K4zuki/tinyI2C/gui/tinyI2Cgui.py

# -*- coding: utf-8 -*-

# Form implementation generated from reading ui file 'tinyI2C.ui'
#
# Created: Mon Feb 02 18:19:01 2015
#      by: PyQt4 UI code generator 4.11.3
#
# WARNING! All changes made in this file will be lost!

from PyQt5 import QtCore, QtGui, QtWidgets

try:
    _fromUtf8 = QtCore.QString.fromUtf8
except AttributeError:
    def _fromUtf8(s):
        return s

try:
    _encoding = QtWidgets.QApplication.UnicodeUTF8

    def _translate(context, text, disambig):
        return QtWidgets.QApplication.translate(context, text, disambig, _encoding)
except AttributeError:
    def _translate(context, text, disambig):
        return QtWidgets.QApplication.translate(context, text, disambig)


class Ui_Form(object):

    def setupUi(self, Form):
        Form.setObjectName(_fromUtf8("Form"))
        Form.resize(726, 826)
        Form.setMaximumSize(QtCore.QSize(1006, 984))
        font = QtGui.QFont()
        font.setPointSize(12)
        Form.setFont(font)
        self.gridLayout = QtWidgets.QGridLayout(Form)
        self.gridLayout.setObjectName(_fromUtf8("gridLayout"))
        self.conport_box = QtWidgets.QGroupBox(Form)
        font = QtGui.QFont()
        font.setPointSize(12)
        self.conport_box.setFont(font)
        self.conport_box.setFlat(False)
        self.conport_box.setCheckable(False)
        self.conport_box.setObjectName(_fromUtf8("conport_box"))
        self.horizontalLayout = QtWidgets.QHBoxLayout(self.conport_box)
        self.horizontalLayout.setObjectName(_fromUtf8("horizontalLayout"))
        self.getPortBtn = QtWidgets.QPushButton(self.conport_box)
        self.getPortBtn.setObjectName(_fromUtf8("getPortBtn"))
        self.horizontalLayout.addWidget(self.getPortBtn)
        self.portList = QtWidgets.QComboBox(self.conport_box)
        font = QtGui.QFont()
        font.setPointSize(12)
        self.portList.setFont(font)
        self.portList.setObjectName(_fromUtf8("portList"))
        self.horizontalLayout.addWidget(self.portList)
        self.gridLayout.addWidget(self.conport_box, 0, 0, 1, 1)
        self.log_box = QtWidgets.QGroupBox(Form)
        font = QtGui.QFont()
        font.setPointSize(12)
        self.log_box.setFont(font)
        self.log_box.setObjectName(_fromUtf8("log_box"))
        self.verticalLayout_9 = QtWidgets.QVBoxLayout(self.log_box)
        self.verticalLayout_9.setObjectName(_fromUtf8("verticalLayout_9"))
        self.log_text = QtWidgets.QPlainTextEdit(self.log_box)
        self.log_text.setVerticalScrollBarPolicy(QtCore.Qt.ScrollBarAlwaysOn)
        self.log_text.setReadOnly(True)
        self.log_text.setCenterOnScroll(True)
        self.log_text.setObjectName(_fromUtf8("log_text"))
        self.verticalLayout_9.addWidget(self.log_text)
        self.gridLayout.addWidget(self.log_box, 5, 0, 1, 1)
        self.i2c_box = QtWidgets.QGroupBox(Form)
        font = QtGui.QFont()
        font.setPointSize(12)
        self.i2c_box.setFont(font)
        self.i2c_box.setObjectName(_fromUtf8("i2c_box"))
        self.horizontalLayout_6 = QtWidgets.QHBoxLayout(self.i2c_box)
        self.horizontalLayout_6.setObjectName(_fromUtf8("horizontalLayout_6"))
        self.i2c1_box = QtWidgets.QGroupBox(self.i2c_box)
        font = QtGui.QFont()
        font.setPointSize(12)
        self.i2c1_box.setFont(font)
        self.i2c1_box.setObjectName(_fromUtf8("i2c1_box"))
        self.verticalLayout = QtWidgets.QVBoxLayout(self.i2c1_box)
        self.verticalLayout.setObjectName(_fromUtf8("verticalLayout"))
        self.base_CH1 = HexSpinBox(self.i2c1_box)
        self.base_CH1.setSuffix(_fromUtf8(""))
        self.base_CH1.setPrefix(_fromUtf8(""))
        self.base_CH1.setMaximum(255)
        self.base_CH1.setSingleStep(2)
        self.base_CH1.setProperty("value", 144)
        self.base_CH1.setObjectName(_fromUtf8("base_CH1"))
        self.verticalLayout.addWidget(self.base_CH1)
        self.reg_CH1 = HexSpinBox(self.i2c1_box)
        self.reg_CH1.setSuffix(_fromUtf8(""))
        self.reg_CH1.setPrefix(_fromUtf8(""))
        self.reg_CH1.setMaximum(255)
        self.reg_CH1.setObjectName(_fromUtf8("reg_CH1"))
        self.verticalLayout.addWidget(self.reg_CH1)
        self.readbtn_CH1 = QtWidgets.QPushButton(self.i2c1_box)
        self.readbtn_CH1.setObjectName(_fromUtf8("readbtn_CH1"))
        self.verticalLayout.addWidget(self.readbtn_CH1)
        self.read_CH1 = HexSpinBox(self.i2c1_box)
        self.read_CH1.setEnabled(False)
        self.read_CH1.setSuffix(_fromUtf8(""))
        self.read_CH1.setPrefix(_fromUtf8(""))
        self.read_CH1.setMaximum(255)
        self.read_CH1.setObjectName(_fromUtf8("read_CH1"))
        self.verticalLayout.addWidget(self.read_CH1)
        self.writebtn_CH1 = QtWidgets.QPushButton(self.i2c1_box)
        self.writebtn_CH1.setObjectName(_fromUtf8("writebtn_CH1"))
        self.verticalLayout.addWidget(self.writebtn_CH1)
        self.write_CH1 = HexSpinBox(self.i2c1_box)
        self.write_CH1.setSuffix(_fromUtf8(""))
        self.write_CH1.setPrefix(_fromUtf8(""))
        self.write_CH1.setMaximum(255)
        self.write_CH1.setObjectName(_fromUtf8("write_CH1"))
        self.verticalLayout.addWidget(self.write_CH1)
        spacerItem = QtWidgets.QSpacerItem(20, 40, QtWidgets.QSizePolicy.Minimum,
                                           QtWidgets.QSizePolicy.MinimumExpanding)
        self.verticalLayout.addItem(spacerItem)
        self.horizontalLayout_6.addWidget(self.i2c1_box)
        self.i2c2_box = QtWidgets.QGroupBox(self.i2c_box)
        font = QtGui.QFont()
        font.setPointSize(12)
        self.i2c2_box.setFont(font)
        self.i2c2_box.setObjectName(_fromUtf8("i2c2_box"))
        self.verticalLayout_5 = QtWidgets.QVBoxLayout(self.i2c2_box)
        self.verticalLayout_5.setObjectName(_fromUtf8("verticalLayout_5"))
        self.base_CH2 = HexSpinBox(self.i2c2_box)
        self.base_CH2.setSuffix(_fromUtf8(""))
        self.base_CH2.setPrefix(_fromUtf8(""))
        self.base_CH2.setMaximum(255)
        self.base_CH2.setSingleStep(2)
        self.base_CH2.setProperty("value", 144)
        self.base_CH2.setObjectName(_fromUtf8("base_CH2"))
        self.verticalLayout_5.addWidget(self.base_CH2)
        self.reg_CH2 = HexSpinBox(self.i2c2_box)
        self.reg_CH2.setSuffix(_fromUtf8(""))
        self.reg_CH2.setPrefix(_fromUtf8(""))
        self.reg_CH2.setMaximum(255)
        self.reg_CH2.setObjectName(_fromUtf8("reg_CH2"))
        self.verticalLayout_5.addWidget(self.reg_CH2)
        self.readbtn_CH2 = QtWidgets.QPushButton(self.i2c2_box)
        self.readbtn_CH2.setObjectName(_fromUtf8("readbtn_CH2"))
        self.verticalLayout_5.addWidget(self.readbtn_CH2)
        self.read_CH2 = HexSpinBox(self.i2c2_box)
        self.read_CH2.setEnabled(False)
        self.read_CH2.setSuffix(_fromUtf8(""))
        self.read_CH2.setPrefix(_fromUtf8(""))
        self.read_CH2.setMaximum(255)
        self.read_CH2.setObjectName(_fromUtf8("read_CH2"))
        self.verticalLayout_5.addWidget(self.read_CH2)
        self.writebtn_CH2 = QtWidgets.QPushButton(self.i2c2_box)
        self.writebtn_CH2.setObjectName(_fromUtf8("writebtn_CH2"))
        self.verticalLayout_5.addWidget(self.writebtn_CH2)
        self.write_CH2 = HexSpinBox(self.i2c2_box)
        self.write_CH2.setSuffix(_fromUtf8(""))
        self.write_CH2.setPrefix(_fromUtf8(""))
        self.write_CH2.setMaximum(255)
        self.write_CH2.setObjectName(_fromUtf8("write_CH2"))
        self.verticalLayout_5.addWidget(self.write_CH2)
        spacerItem1 = QtWidgets.QSpacerItem(20, 40, QtWidgets.QSizePolicy.Minimum,
                                            QtWidgets.QSizePolicy.MinimumExpanding)
        self.verticalLayout_5.addItem(spacerItem1)
        self.horizontalLayout_6.addWidget(self.i2c2_box)
        self.i2c3_box = QtWidgets.QGroupBox(self.i2c_box)
        font = QtGui.QFont()
        font.setPointSize(12)
        self.i2c3_box.setFont(font)
        self.i2c3_box.setObjectName(_fromUtf8("i2c3_box"))
        self.verticalLayout_6 = QtWidgets.QVBoxLayout(self.i2c3_box)
        self.verticalLayout_6.setObjectName(_fromUtf8("verticalLayout_6"))
        self.base_CH3 = HexSpinBox(self.i2c3_box)
        self.base_CH3.setSuffix(_fromUtf8(""))
        self.base_CH3.setPrefix(_fromUtf8(""))
        self.base_CH3.setMaximum(255)
        self.base_CH3.setSingleStep(2)
        self.base_CH3.setProperty("value", 144)
        self.base_CH3.setObjectName(_fromUtf8("base_CH3"))
        self.verticalLayout_6.addWidget(self.base_CH3)
        self.reg_CH3 = HexSpinBox(self.i2c3_box)
        self.reg_CH3.setSuffix(_fromUtf8(""))
        self.reg_CH3.setPrefix(_fromUtf8(""))
        self.reg_CH3.setMaximum(255)
        self.reg_CH3.setObjectName(_fromUtf8("reg_CH3"))
        self.verticalLayout_6.addWidget(self.reg_CH3)
        self.readbtn_CH3 = QtWidgets.QPushButton(self.i2c3_box)
        self.readbtn_CH3.setObjectName(_fromUtf8("readbtn_CH3"))
        self.verticalLayout_6.addWidget(self.readbtn_CH3)
        self.read_CH3 = HexSpinBox(self.i2c3_box)
        self.read_CH3.setEnabled(False)
        self.read_CH3.setSuffix(_fromUtf8(""))
        self.read_CH3.setPrefix(_fromUtf8(""))
        self.read_CH3.setMaximum(255)
        self.read_CH3.setObjectName(_fromUtf8("read_CH3"))
        self.verticalLayout_6.addWidget(self.read_CH3)
        self.writebtn_CH3 = QtWidgets.QPushButton(self.i2c3_box)
        self.writebtn_CH3.setObjectName(_fromUtf8("writebtn_CH3"))
        self.verticalLayout_6.addWidget(self.writebtn_CH3)
        self.write_CH3 = HexSpinBox(self.i2c3_box)
        self.write_CH3.setSuffix(_fromUtf8(""))
        self.write_CH3.setPrefix(_fromUtf8(""))
        self.write_CH3.setMaximum(255)
        self.write_CH3.setObjectName(_fromUtf8("write_CH3"))
        self.verticalLayout_6.addWidget(self.write_CH3)
        spacerItem2 = QtWidgets.QSpacerItem(20, 40, QtWidgets.QSizePolicy.Minimum, QtWidgets.QSizePolicy.Expanding)
        self.verticalLayout_6.addItem(spacerItem2)
        self.horizontalLayout_6.addWidget(self.i2c3_box)
        self.i2c4_box = QtWidgets.QGroupBox(self.i2c_box)
        font = QtGui.QFont()
        font.setPointSize(12)
        self.i2c4_box.setFont(font)
        self.i2c4_box.setObjectName(_fromUtf8("i2c4_box"))
        self.verticalLayout_7 = QtWidgets.QVBoxLayout(self.i2c4_box)
        self.verticalLayout_7.setObjectName(_fromUtf8("verticalLayout_7"))
        self.base_CH4 = HexSpinBox(self.i2c4_box)
        self.base_CH4.setSuffix(_fromUtf8(""))
        self.base_CH4.setPrefix(_fromUtf8(""))
        self.base_CH4.setMaximum(255)
        self.base_CH4.setSingleStep(2)
        self.base_CH4.setProperty("value", 144)
        self.base_CH4.setObjectName(_fromUtf8("base_CH4"))
        self.verticalLayout_7.addWidget(self.base_CH4)
        self.reg_CH4 = HexSpinBox(self.i2c4_box)
        self.reg_CH4.setSuffix(_fromUtf8(""))
        self.reg_CH4.setPrefix(_fromUtf8(""))
        self.reg_CH4.setMaximum(255)
        self.reg_CH4.setObjectName(_fromUtf8("reg_CH4"))
        self.verticalLayout_7.addWidget(self.reg_CH4)
        self.readbtn_CH4 = QtWidgets.QPushButton(self.i2c4_box)
        self.readbtn_CH4.setObjectName(_fromUtf8("readbtn_CH4"))
        self.verticalLayout_7.addWidget(self.readbtn_CH4)
        self.read_CH4 = HexSpinBox(self.i2c4_box)
        self.read_CH4.setEnabled(False)
        self.read_CH4.setSuffix(_fromUtf8(""))
        self.read_CH4.setPrefix(_fromUtf8(""))
        self.read_CH4.setMaximum(255)
        self.read_CH4.setObjectName(_fromUtf8("read_CH4"))
        self.verticalLayout_7.addWidget(self.read_CH4)
        self.writebtn_CH4 = QtWidgets.QPushButton(self.i2c4_box)
        self.writebtn_CH4.setObjectName(_fromUtf8("writebtn_CH4"))
        self.verticalLayout_7.addWidget(self.writebtn_CH4)
        self.write_CH4 = HexSpinBox(self.i2c4_box)
        self.write_CH4.setSuffix(_fromUtf8(""))
        self.write_CH4.setPrefix(_fromUtf8(""))
        self.write_CH4.setMaximum(255)
        self.write_CH4.setObjectName(_fromUtf8("write_CH4"))
        self.verticalLayout_7.addWidget(self.write_CH4)
        spacerItem3 = QtWidgets.QSpacerItem(20, 40, QtWidgets.QSizePolicy.Minimum, QtWidgets.QSizePolicy.Expanding)
        self.verticalLayout_7.addItem(spacerItem3)
        self.horizontalLayout_6.addWidget(self.i2c4_box)
        self.spi_box = QtWidgets.QGroupBox(self.i2c_box)
        font = QtGui.QFont()
        font.setPointSize(12)
        self.spi_box.setFont(font)
        self.spi_box.setObjectName(_fromUtf8("spi_box"))
        self.verticalLayout_10 = QtWidgets.QVBoxLayout(self.spi_box)
        self.verticalLayout_10.setObjectName(_fromUtf8("verticalLayout_10"))
        self.base_SPI = HexSpinBox(self.spi_box)
        self.base_SPI.setSuffix(_fromUtf8(""))
        self.base_SPI.setPrefix(_fromUtf8(""))
        self.base_SPI.setMaximum(255)
        self.base_SPI.setProperty("value", 144)
        self.base_SPI.setObjectName(_fromUtf8("base_SPI"))
        self.verticalLayout_10.addWidget(self.base_SPI)
        self.reg_SPI = HexSpinBox(self.spi_box)
        self.reg_SPI.setSuffix(_fromUtf8(""))
        self.reg_SPI.setPrefix(_fromUtf8(""))
        self.reg_SPI.setMaximum(255)
        self.reg_SPI.setObjectName(_fromUtf8("reg_SPI"))
        self.verticalLayout_10.addWidget(self.reg_SPI)
        self.readbtn_SPI = QtWidgets.QPushButton(self.spi_box)
        self.readbtn_SPI.setObjectName(_fromUtf8("readbtn_SPI"))
        self.verticalLayout_10.addWidget(self.readbtn_SPI)
        self.read_SPI = HexSpinBox(self.spi_box)
        self.read_SPI.setEnabled(False)
        self.read_SPI.setSuffix(_fromUtf8(""))
        self.read_SPI.setPrefix(_fromUtf8(""))
        self.read_SPI.setMaximum(255)
        self.read_SPI.setObjectName(_fromUtf8("read_SPI"))
        self.verticalLayout_10.addWidget(self.read_SPI)
        self.writebtn_SPI = QtWidgets.QPushButton(self.spi_box)
        self.writebtn_SPI.setObjectName(_fromUtf8("writebtn_SPI"))
        self.verticalLayout_10.addWidget(self.writebtn_SPI)
        self.write_SPI = HexSpinBox(self.spi_box)
        self.write_SPI.setSuffix(_fromUtf8(""))
        self.write_SPI.setPrefix(_fromUtf8(""))
        self.write_SPI.setMaximum(255)
        self.write_SPI.setObjectName(_fromUtf8("write_SPI"))
        self.verticalLayout_10.addWidget(self.write_SPI)
        spacerItem4 = QtWidgets.QSpacerItem(20, 40, QtWidgets.QSizePolicy.Minimum, QtWidgets.QSizePolicy.Expanding)
        self.verticalLayout_10.addItem(spacerItem4)
        self.horizontalLayout_6.addWidget(self.spi_box)
        self.gridLayout.addWidget(self.i2c_box, 1, 0, 1, 1)
        self.regixters_box = QtWidgets.QGroupBox(Form)
        self.regixters_box.setObjectName(_fromUtf8("regixters_box"))
        self.verticalLayout_2 = QtWidgets.QVBoxLayout(self.regixters_box)
        self.verticalLayout_2.setObjectName(_fromUtf8("verticalLayout_2"))
        self.registers_tab = QtWidgets.QTabWidget(self.regixters_box)
        self.registers_tab.setObjectName(_fromUtf8("registers_tab"))
        self.tab = QtWidgets.QWidget()
        self.tab.setObjectName(_fromUtf8("tab"))
        self.verticalLayout_11 = QtWidgets.QVBoxLayout(self.tab)
        self.verticalLayout_11.setObjectName(_fromUtf8("verticalLayout_11"))
        self.reg0_box = QtWidgets.QGroupBox(self.tab)
        self.reg0_box.setObjectName(_fromUtf8("reg0_box"))
        self.gridLayout_2 = QtWidgets.QGridLayout(self.reg0_box)
        self.gridLayout_2.setObjectName(_fromUtf8("gridLayout_2"))
        self.readbtn_reg0 = QtWidgets.QPushButton(self.reg0_box)
        self.readbtn_reg0.setObjectName(_fromUtf8("readbtn_reg0"))
        self.gridLayout_2.addWidget(self.readbtn_reg0, 1, 8, 1, 1)
        self.read_reg0 = HexSpinBox(self.reg0_box)
        self.read_reg0.setEnabled(False)
        self.read_reg0.setMaximum(255)
        self.read_reg0.setObjectName(_fromUtf8("read_reg0"))
        self.gridLayout_2.addWidget(self.read_reg0, 1, 9, 1, 1)
        self.writebtn_reg0 = QtWidgets.QPushButton(self.reg0_box)
        self.writebtn_reg0.setEnabled(False)
        self.writebtn_reg0.setObjectName(_fromUtf8("writebtn_reg0"))
        self.gridLayout_2.addWidget(self.writebtn_reg0, 1, 10, 1, 1)
        self.write_reg0 = HexSpinBox(self.reg0_box)
        self.write_reg0.setEnabled(False)
        self.write_reg0.setMaximum(255)
        self.write_reg0.setObjectName(_fromUtf8("write_reg0"))
        self.gridLayout_2.addWidget(self.write_reg0, 1, 11, 1, 1)
        self.label_8 = QtWidgets.QLabel(self.reg0_box)
        self.label_8.setAlignment(QtCore.Qt.AlignCenter)
        self.label_8.setObjectName(_fromUtf8("label_8"))
        self.gridLayout_2.addWidget(self.label_8, 0, 7, 1, 1)
        self.label = QtWidgets.QLabel(self.reg0_box)
        self.label.setAlignment(QtCore.Qt.AlignCenter)
        self.label.setObjectName(_fromUtf8("label"))
        self.gridLayout_2.addWidget(self.label, 0, 0, 1, 1)
        self.label_7 = QtWidgets.QLabel(self.reg0_box)
        self.label_7.setAlignment(QtCore.Qt.AlignCenter)
        self.label_7.setObjectName(_fromUtf8("label_7"))
        self.gridLayout_2.addWidget(self.label_7, 0, 6, 1, 1)
        self.label_6 = QtWidgets.QLabel(self.reg0_box)
        self.label_6.setAlignment(QtCore.Qt.AlignCenter)
        self.label_6.setObjectName(_fromUtf8("label_6"))
        self.gridLayout_2.addWidget(self.label_6, 0, 5, 1, 1)
        self.label_5 = QtWidgets.QLabel(self.reg0_box)
        self.label_5.setAlignment(QtCore.Qt.AlignCenter)
        self.label_5.setObjectName(_fromUtf8("label_5"))
        self.gridLayout_2.addWidget(self.label_5, 0, 4, 1, 1)
        self.label_4 = QtWidgets.QLabel(self.reg0_box)
        self.label_4.setAlignment(QtCore.Qt.AlignCenter)
        self.label_4.setObjectName(_fromUtf8("label_4"))
        self.gridLayout_2.addWidget(self.label_4, 0, 3, 1, 1)
        self.label_3 = QtWidgets.QLabel(self.reg0_box)
        self.label_3.setAlignment(QtCore.Qt.AlignCenter)
        self.label_3.setObjectName(_fromUtf8("label_3"))
        self.gridLayout_2.addWidget(self.label_3, 0, 2, 1, 1)
        self.label_2 = QtWidgets.QLabel(self.reg0_box)
        self.label_2.setAlignment(QtCore.Qt.AlignCenter)
        self.label_2.setObjectName(_fromUtf8("label_2"))
        self.gridLayout_2.addWidget(self.label_2, 0, 1, 1, 1)
        self.reg00 = QtWidgets.QPushButton(self.reg0_box)
        self.reg00.setEnabled(False)
        self.reg00.setMinimumSize(QtCore.QSize(40, 0))
        font = QtGui.QFont()
        font.setPointSize(20)
        self.reg00.setFont(font)
        self.reg00.setCheckable(True)
        self.reg00.setFlat(True)
        self.reg00.setObjectName(_fromUtf8("reg00"))
        self.gridLayout_2.addWidget(self.reg00, 1, 7, 1, 1)
        self.reg01 = QtWidgets.QPushButton(self.reg0_box)
        self.reg01.setEnabled(False)
        self.reg01.setMinimumSize(QtCore.QSize(40, 0))
        font = QtGui.QFont()
        font.setPointSize(20)
        self.reg01.setFont(font)
        self.reg01.setCheckable(True)
        self.reg01.setFlat(True)
        self.reg01.setObjectName(_fromUtf8("reg01"))
        self.gridLayout_2.addWidget(self.reg01, 1, 6, 1, 1)
        self.reg02 = QtWidgets.QPushButton(self.reg0_box)
        self.reg02.setEnabled(False)
        self.reg02.setMinimumSize(QtCore.QSize(40, 0))
        font = QtGui.QFont()
        font.setPointSize(20)
        self.reg02.setFont(font)
        self.reg02.setCheckable(True)
        self.reg02.setFlat(True)
        self.reg02.setObjectName(_fromUtf8("reg02"))
        self.gridLayout_2.addWidget(self.reg02, 1, 5, 1, 1)
        self.reg03 = QtWidgets.QPushButton(self.reg0_box)
        self.reg03.setEnabled(False)
        self.reg03.setMinimumSize(QtCore.QSize(40, 0))
        font = QtGui.QFont()
        font.setPointSize(20)
        self.reg03.setFont(font)
        self.reg03.setCheckable(True)
        self.reg03.setFlat(True)
        self.reg03.setObjectName(_fromUtf8("reg03"))
        self.gridLayout_2.addWidget(self.reg03, 1, 4, 1, 1)
        self.reg04 = QtWidgets.QPushButton(self.reg0_box)
        self.reg04.setEnabled(False)
        self.reg04.setMinimumSize(QtCore.QSize(40, 0))
        font = QtGui.QFont()
        font.setPointSize(20)
        self.reg04.setFont(font)
        self.reg04.setCheckable(True)
        self.reg04.setFlat(True)
        self.reg04.setObjectName(_fromUtf8("reg04"))
        self.gridLayout_2.addWidget(self.reg04, 1, 3, 1, 1)
        self.reg05 = QtWidgets.QPushButton(self.reg0_box)
        self.reg05.setEnabled(False)
        self.reg05.setMinimumSize(QtCore.QSize(40, 0))
        font = QtGui.QFont()
        font.setPointSize(20)
        self.reg05.setFont(font)
        self.reg05.setCheckable(True)
        self.reg05.setFlat(True)
        self.reg05.setObjectName(_fromUtf8("reg05"))
        self.gridLayout_2.addWidget(self.reg05, 1, 2, 1, 1)
        self.reg06 = QtWidgets.QPushButton(self.reg0_box)
        self.reg06.setEnabled(False)
        self.reg06.setMinimumSize(QtCore.QSize(40, 0))
        font = QtGui.QFont()
        font.setPointSize(20)
        self.reg06.setFont(font)
        self.reg06.setCheckable(True)
        self.reg06.setFlat(True)
        self.reg06.setObjectName(_fromUtf8("reg06"))
        self.gridLayout_2.addWidget(self.reg06, 1, 1, 1, 1)
        self.reg07 = QtWidgets.QPushButton(self.reg0_box)
        self.reg07.setEnabled(False)
        self.reg07.setMinimumSize(QtCore.QSize(40, 0))
        font = QtGui.QFont()
        font.setPointSize(20)
        self.reg07.setFont(font)
        self.reg07.setCheckable(True)
        self.reg07.setFlat(True)
        self.reg07.setObjectName(_fromUtf8("reg07"))
        self.gridLayout_2.addWidget(self.reg07, 1, 0, 1, 1)
        self.verticalLayout_11.addWidget(self.reg0_box)
        self.groupBox = QtWidgets.QGroupBox(self.tab)
        self.groupBox.setTitle(_fromUtf8(""))
        self.groupBox.setObjectName(_fromUtf8("groupBox"))
        self.horizontalLayout_2 = QtWidgets.QHBoxLayout(self.groupBox)
        self.horizontalLayout_2.setObjectName(_fromUtf8("horizontalLayout_2"))
        self.verticalLayout_11.addWidget(self.groupBox)
        self.registers_tab.addTab(self.tab, _fromUtf8(""))
        self.tab_2 = QtWidgets.QWidget()
        self.tab_2.setObjectName(_fromUtf8("tab_2"))
        self.verticalLayout_8 = QtWidgets.QVBoxLayout(self.tab_2)
        self.verticalLayout_8.setObjectName(_fromUtf8("verticalLayout_8"))
        self.reg1_box = QtWidgets.QGroupBox(self.tab_2)
        self.reg1_box.setObjectName(_fromUtf8("reg1_box"))
        self.gridLayout_3 = QtWidgets.QGridLayout(self.reg1_box)
        self.gridLayout_3.setObjectName(_fromUtf8("gridLayout_3"))
        self.label_15 = QtWidgets.QLabel(self.reg1_box)
        self.label_15.setAlignment(QtCore.Qt.AlignCenter)
        self.label_15.setObjectName(_fromUtf8("label_15"))
        self.gridLayout_3.addWidget(self.label_15, 0, 0, 1, 1)
        self.label_13 = QtWidgets.QLabel(self.reg1_box)
        self.label_13.setAlignment(QtCore.Qt.AlignCenter)
        self.label_13.setObjectName(_fromUtf8("label_13"))
        self.gridLayout_3.addWidget(self.label_13, 0, 1, 1, 1)
        self.label_16 = QtWidgets.QLabel(self.reg1_box)
        self.label_16.setAlignment(QtCore.Qt.AlignCenter)
        self.label_16.setObjectName(_fromUtf8("label_16"))
        self.gridLayout_3.addWidget(self.label_16, 0, 2, 1, 1)
        self.label_12 = QtWidgets.QLabel(self.reg1_box)
        self.label_12.setAlignment(QtCore.Qt.AlignCenter)
        self.label_12.setObjectName(_fromUtf8("label_12"))
        self.gridLayout_3.addWidget(self.label_12, 0, 3, 1, 1)
        self.label_9 = QtWidgets.QLabel(self.reg1_box)
        self.label_9.setAlignment(QtCore.Qt.AlignCenter)
        self.label_9.setObjectName(_fromUtf8("label_9"))
        self.gridLayout_3.addWidget(self.label_9, 0, 4, 1, 1)
        self.label_14 = QtWidgets.QLabel(self.reg1_box)
        self.label_14.setAlignment(QtCore.Qt.AlignCenter)
        self.label_14.setObjectName(_fromUtf8("label_14"))
        self.gridLayout_3.addWidget(self.label_14, 0, 5, 1, 1)
        self.label_11 = QtWidgets.QLabel(self.reg1_box)
        self.label_11.setAlignment(QtCore.Qt.AlignCenter)
        self.label_11.setObjectName(_fromUtf8("label_11"))
        self.gridLayout_3.addWidget(self.label_11, 0, 6, 1, 1)
        self.label_10 = QtWidgets.QLabel(self.reg1_box)
        self.label_10.setAlignment(QtCore.Qt.AlignCenter)
        self.label_10.setObjectName(_fromUtf8("label_10"))
        self.gridLayout_3.addWidget(self.label_10, 0, 7, 1, 1)
        self.reg17 = QtWidgets.QPushButton(self.reg1_box)
        self.reg17.setEnabled(True)
        self.reg17.setMinimumSize(QtCore.QSize(40, 0))
        font = QtGui.QFont()
        font.setPointSize(20)
        self.reg17.setFont(font)
        self.reg17.setCheckable(True)
        self.reg17.setFlat(True)
        self.reg17.setObjectName(_fromUtf8("reg17"))
        self.gridLayout_3.addWidget(self.reg17, 1, 0, 1, 1)
        self.reg16 = QtWidgets.QPushButton(self.reg1_box)
        self.reg16.setEnabled(True)
        self.reg16.setMinimumSize(QtCore.QSize(40, 0))
        font = QtGui.QFont()
        font.setPointSize(20)
        self.reg16.setFont(font)
        self.reg16.setCheckable(True)
        self.reg16.setFlat(True)
        self.reg16.setObjectName(_fromUtf8("reg16"))
        self.gridLayout_3.addWidget(self.reg16, 1, 1, 1, 1)
        self.reg15 = QtWidgets.QPushButton(self.reg1_box)
        self.reg15.setEnabled(True)
        self.reg15.setMinimumSize(QtCore.QSize(40, 0))
        font = QtGui.QFont()
        font.setPointSize(20)
        self.reg15.setFont(font)
        self.reg15.setCheckable(True)
        self.reg15.setFlat(True)
        self.reg15.setObjectName(_fromUtf8("reg15"))
        self.gridLayout_3.addWidget(self.reg15, 1, 2, 1, 1)
        self.reg14 = QtWidgets.QPushButton(self.reg1_box)
        self.reg14.setEnabled(True)
        self.reg14.setMinimumSize(QtCore.QSize(40, 0))
        font = QtGui.QFont()
        font.setPointSize(20)
        self.reg14.setFont(font)
        self.reg14.setCheckable(True)
        self.reg14.setFlat(True)
        self.reg14.setObjectName(_fromUtf8("reg14"))
        self.gridLayout_3.addWidget(self.reg14, 1, 3, 1, 1)
        self.reg13 = QtWidgets.QPushButton(self.reg1_box)
        self.reg13.setEnabled(True)
        self.reg13.setMinimumSize(QtCore.QSize(40, 0))
        font = QtGui.QFont()
        font.setPointSize(20)
        self.reg13.setFont(font)
        self.reg13.setCheckable(True)
        self.reg13.setFlat(True)
        self.reg13.setObjectName(_fromUtf8("reg13"))
        self.gridLayout_3.addWidget(self.reg13, 1, 4, 1, 1)
        self.reg12 = QtWidgets.QPushButton(self.reg1_box)
        self.reg12.setEnabled(True)
        self.reg12.setMinimumSize(QtCore.QSize(40, 0))
        font = QtGui.QFont()
        font.setPointSize(20)
        self.reg12.setFont(font)
        self.reg12.setCheckable(True)
        self.reg12.setFlat(True)
        self.reg12.setObjectName(_fromUtf8("reg12"))
        self.gridLayout_3.addWidget(self.reg12, 1, 5, 1, 1)
        self.reg11 = QtWidgets.QPushButton(self.reg1_box)
        self.reg11.setEnabled(True)
        self.reg11.setMinimumSize(QtCore.QSize(40, 0))
        font = QtGui.QFont()
        font.setPointSize(20)
        self.reg11.setFont(font)
        self.reg11.setCheckable(True)
        self.reg11.setFlat(True)
        self.reg11.setObjectName(_fromUtf8("reg11"))
        self.gridLayout_3.addWidget(self.reg11, 1, 6, 1, 1)
        self.reg10 = QtWidgets.QPushButton(self.reg1_box)
        self.reg10.setEnabled(True)
        self.reg10.setMinimumSize(QtCore.QSize(40, 0))
        font = QtGui.QFont()
        font.setPointSize(20)
        self.reg10.setFont(font)
        self.reg10.setCheckable(True)
        self.reg10.setFlat(True)
        self.reg10.setObjectName(_fromUtf8("reg10"))
        self.gridLayout_3.addWidget(self.reg10, 1, 7, 1, 1)
        self.readbtn_reg1 = QtWidgets.QPushButton(self.reg1_box)
        self.readbtn_reg1.setObjectName(_fromUtf8("readbtn_reg1"))
        self.gridLayout_3.addWidget(self.readbtn_reg1, 1, 8, 1, 1)
        self.read_reg1 = HexSpinBox(self.reg1_box)
        self.read_reg1.setEnabled(False)
        self.read_reg1.setMaximum(255)
        self.read_reg1.setObjectName(_fromUtf8("read_reg1"))
        self.gridLayout_3.addWidget(self.read_reg1, 1, 9, 1, 1)
        self.writebtn_reg1 = QtWidgets.QPushButton(self.reg1_box)
        self.writebtn_reg1.setObjectName(_fromUtf8("writebtn_reg1"))
        self.gridLayout_3.addWidget(self.writebtn_reg1, 1, 10, 1, 1)
        self.write_reg1 = HexSpinBox(self.reg1_box)
        self.write_reg1.setMaximum(255)
        self.write_reg1.setObjectName(_fromUtf8("write_reg1"))
        self.gridLayout_3.addWidget(self.write_reg1, 1, 11, 1, 1)
        self.verticalLayout_8.addWidget(self.reg1_box)
        self.reg3_box = QtWidgets.QGroupBox(self.tab_2)
        self.reg3_box.setObjectName(_fromUtf8("reg3_box"))
        self.gridLayout_7 = QtWidgets.QGridLayout(self.reg3_box)
        self.gridLayout_7.setObjectName(_fromUtf8("gridLayout_7"))
        self.label_47 = QtWidgets.QLabel(self.reg3_box)
        self.label_47.setAlignment(QtCore.Qt.AlignCenter)
        self.label_47.setObjectName(_fromUtf8("label_47"))
        self.gridLayout_7.addWidget(self.label_47, 0, 0, 1, 1)
        self.label_48 = QtWidgets.QLabel(self.reg3_box)
        self.label_48.setAlignment(QtCore.Qt.AlignCenter)
        self.label_48.setObjectName(_fromUtf8("label_48"))
        self.gridLayout_7.addWidget(self.label_48, 0, 2, 1, 1)
        self.label_46 = QtWidgets.QLabel(self.reg3_box)
        self.label_46.setAlignment(QtCore.Qt.AlignCenter)
        self.label_46.setObjectName(_fromUtf8("label_46"))
        self.gridLayout_7.addWidget(self.label_46, 0, 5, 1, 1)
        self.reg36 = QtWidgets.QPushButton(self.reg3_box)
        self.reg36.setMinimumSize(QtCore.QSize(40, 0))
        font = QtGui.QFont()
        font.setPointSize(20)
        self.reg36.setFont(font)
        self.reg36.setCheckable(True)
        self.reg36.setFlat(True)
        self.reg36.setObjectName(_fromUtf8("reg36"))
        self.gridLayout_7.addWidget(self.reg36, 2, 1, 1, 1)
        self.reg35 = QtWidgets.QPushButton(self.reg3_box)
        self.reg35.setMinimumSize(QtCore.QSize(40, 0))
        font = QtGui.QFont()
        font.setPointSize(20)
        self.reg35.setFont(font)
        self.reg35.setCheckable(True)
        self.reg35.setFlat(True)
        self.reg35.setObjectName(_fromUtf8("reg35"))
        self.gridLayout_7.addWidget(self.reg35, 2, 2, 1, 1)
        self.reg34 = QtWidgets.QPushButton(self.reg3_box)
        self.reg34.setMinimumSize(QtCore.QSize(40, 0))
        font = QtGui.QFont()
        font.setPointSize(20)
        self.reg34.setFont(font)
        self.reg34.setCheckable(True)
        self.reg34.setFlat(True)
        self.reg34.setObjectName(_fromUtf8("reg34"))
        self.gridLayout_7.addWidget(self.reg34, 2, 3, 1, 1)
        self.label_41 = QtWidgets.QLabel(self.reg3_box)
        self.label_41.setAlignment(QtCore.Qt.AlignCenter)
        self.label_41.setObjectName(_fromUtf8("label_41"))
        self.gridLayout_7.addWidget(self.label_41, 0, 4, 1, 1)
        self.label_45 = QtWidgets.QLabel(self.reg3_box)
        self.label_45.setAlignment(QtCore.Qt.AlignCenter)
        self.label_45.setObjectName(_fromUtf8("label_45"))
        self.gridLayout_7.addWidget(self.label_45, 0, 1, 1, 1)
        self.write_reg3 = HexSpinBox(self.reg3_box)
        self.write_reg3.setMaximum(255)
        self.write_reg3.setObjectName(_fromUtf8("write_reg3"))
        self.gridLayout_7.addWidget(self.write_reg3, 2, 17, 1, 1)
        self.writebtn_reg3 = QtWidgets.QPushButton(self.reg3_box)
        self.writebtn_reg3.setObjectName(_fromUtf8("writebtn_reg3"))
        self.gridLayout_7.addWidget(self.writebtn_reg3, 2, 16, 1, 1)
        self.readbtn_reg3 = QtWidgets.QPushButton(self.reg3_box)
        self.readbtn_reg3.setObjectName(_fromUtf8("readbtn_reg3"))
        self.gridLayout_7.addWidget(self.readbtn_reg3, 2, 14, 1, 1)
        self.read_reg3 = HexSpinBox(self.reg3_box)
        self.read_reg3.setEnabled(False)
        self.read_reg3.setMaximum(255)
        self.read_reg3.setObjectName(_fromUtf8("read_reg3"))
        self.gridLayout_7.addWidget(self.read_reg3, 2, 15, 1, 1)
        self.label_44 = QtWidgets.QLabel(self.reg3_box)
        self.label_44.setAlignment(QtCore.Qt.AlignCenter)
        self.label_44.setObjectName(_fromUtf8("label_44"))
        self.gridLayout_7.addWidget(self.label_44, 0, 3, 1, 1)
        self.reg30 = QtWidgets.QPushButton(self.reg3_box)
        self.reg30.setMinimumSize(QtCore.QSize(40, 0))
        font = QtGui.QFont()
        font.setPointSize(20)
        self.reg30.setFont(font)
        self.reg30.setCheckable(True)
        self.reg30.setFlat(True)
        self.reg30.setObjectName(_fromUtf8("reg30"))
        self.gridLayout_7.addWidget(self.reg30, 2, 7, 1, 1)
        self.reg33 = QtWidgets.QPushButton(self.reg3_box)
        self.reg33.setMinimumSize(QtCore.QSize(40, 0))
        font = QtGui.QFont()
        font.setPointSize(20)
        self.reg33.setFont(font)
        self.reg33.setCheckable(True)
        self.reg33.setFlat(True)
        self.reg33.setObjectName(_fromUtf8("reg33"))
        self.gridLayout_7.addWidget(self.reg33, 2, 4, 1, 1)
        self.label_42 = QtWidgets.QLabel(self.reg3_box)
        self.label_42.setAlignment(QtCore.Qt.AlignCenter)
        self.label_42.setObjectName(_fromUtf8("label_42"))
        self.gridLayout_7.addWidget(self.label_42, 0, 7, 1, 1)
        self.label_43 = QtWidgets.QLabel(self.reg3_box)
        self.label_43.setAlignment(QtCore.Qt.AlignCenter)
        self.label_43.setObjectName(_fromUtf8("label_43"))
        self.gridLayout_7.addWidget(self.label_43, 0, 6, 1, 1)
        self.reg32 = QtWidgets.QPushButton(self.reg3_box)
        self.reg32.setMinimumSize(QtCore.QSize(40, 0))
        font = QtGui.QFont()
        font.setPointSize(20)
        self.reg32.setFont(font)
        self.reg32.setCheckable(True)
        self.reg32.setFlat(True)
        self.reg32.setObjectName(_fromUtf8("reg32"))
        self.gridLayout_7.addWidget(self.reg32, 2, 5, 1, 1)
        self.reg31 = QtWidgets.QPushButton(self.reg3_box)
        self.reg31.setMinimumSize(QtCore.QSize(40, 0))
        font = QtGui.QFont()
        font.setPointSize(20)
        self.reg31.setFont(font)
        self.reg31.setCheckable(True)
        self.reg31.setFlat(True)
        self.reg31.setObjectName(_fromUtf8("reg31"))
        self.gridLayout_7.addWidget(self.reg31, 2, 6, 1, 1)
        self.reg37 = QtWidgets.QPushButton(self.reg3_box)
        self.reg37.setMinimumSize(QtCore.QSize(40, 0))
        font = QtGui.QFont()
        font.setPointSize(20)
        self.reg37.setFont(font)
        self.reg37.setCheckable(True)
        self.reg37.setFlat(True)
        self.reg37.setObjectName(_fromUtf8("reg37"))
        self.gridLayout_7.addWidget(self.reg37, 2, 0, 1, 1)
        self.verticalLayout_8.addWidget(self.reg3_box)
        self.registers_tab.addTab(self.tab_2, _fromUtf8(""))
        self.tab_3 = QtWidgets.QWidget()
        self.tab_3.setObjectName(_fromUtf8("tab_3"))
        self.verticalLayout_3 = QtWidgets.QVBoxLayout(self.tab_3)
        self.verticalLayout_3.setObjectName(_fromUtf8("verticalLayout_3"))
        self.groupBox_14 = QtWidgets.QGroupBox(self.tab_3)
        self.groupBox_14.setEnabled(False)
        self.groupBox_14.setObjectName(_fromUtf8("groupBox_14"))
        self.gridLayout_6 = QtWidgets.QGridLayout(self.groupBox_14)
        self.gridLayout_6.setObjectName(_fromUtf8("gridLayout_6"))
        self.label_37 = QtWidgets.QLabel(self.groupBox_14)
        self.label_37.setAlignment(QtCore.Qt.AlignCenter)
        self.label_37.setObjectName(_fromUtf8("label_37"))
        self.gridLayout_6.addWidget(self.label_37, 1, 1, 1, 1)
        self.label_40 = QtWidgets.QLabel(self.groupBox_14)
        self.label_40.setAlignment(QtCore.Qt.AlignCenter)
        self.label_40.setObjectName(_fromUtf8("label_40"))
        self.gridLayout_6.addWidget(self.label_40, 1, 2, 1, 1)
        self.label_36 = QtWidgets.QLabel(self.groupBox_14)
        self.label_36.setAlignment(QtCore.Qt.AlignCenter)
        self.label_36.setObjectName(_fromUtf8("label_36"))
        self.gridLayout_6.addWidget(self.label_36, 1, 3, 1, 1)
        self.label_33 = QtWidgets.QLabel(self.groupBox_14)
        self.label_33.setAlignment(QtCore.Qt.AlignCenter)
        self.label_33.setObjectName(_fromUtf8("label_33"))
        self.gridLayout_6.addWidget(self.label_33, 1, 4, 1, 1)
        self.label_38 = QtWidgets.QLabel(self.groupBox_14)
        self.label_38.setAlignment(QtCore.Qt.AlignCenter)
        self.label_38.setObjectName(_fromUtf8("label_38"))
        self.gridLayout_6.addWidget(self.label_38, 1, 5, 1, 1)
        self.label_35 = QtWidgets.QLabel(self.groupBox_14)
        self.label_35.setAlignment(QtCore.Qt.AlignCenter)
        self.label_35.setObjectName(_fromUtf8("label_35"))
        self.gridLayout_6.addWidget(self.label_35, 1, 6, 1, 1)
        self.label_34 = QtWidgets.QLabel(self.groupBox_14)
        self.label_34.setAlignment(QtCore.Qt.AlignCenter)
        self.label_34.setObjectName(_fromUtf8("label_34"))
        self.gridLayout_6.addWidget(self.label_34, 1, 7, 1, 1)
        self.reg22 = QtWidgets.QPushButton(self.groupBox_14)
        self.reg22.setMinimumSize(QtCore.QSize(40, 0))
        font = QtGui.QFont()
        font.setPointSize(20)
        self.reg22.setFont(font)
        self.reg22.setCheckable(True)
        self.reg22.setFlat(True)
        self.reg22.setObjectName(_fromUtf8("reg22"))
        self.gridLayout_6.addWidget(self.reg22, 3, 5, 1, 1)
        self.spinBox_11 = HexSpinBox(self.groupBox_14)
        self.spinBox_11.setMaximum(255)
        self.spinBox_11.setObjectName(_fromUtf8("spinBox_11"))
        self.gridLayout_6.addWidget(self.spinBox_11, 3, 11, 1, 1)
        self.reg24 = QtWidgets.QPushButton(self.groupBox_14)
        self.reg24.setMinimumSize(QtCore.QSize(40, 0))
        font = QtGui.QFont()
        font.setPointSize(20)
        self.reg24.setFont(font)
        self.reg24.setCheckable(True)
        self.reg24.setFlat(True)
        self.reg24.setObjectName(_fromUtf8("reg24"))
        self.gridLayout_6.addWidget(self.reg24, 3, 3, 1, 1)
        self.reg25 = QtWidgets.QPushButton(self.groupBox_14)
        self.reg25.setMinimumSize(QtCore.QSize(40, 0))
        font = QtGui.QFont()
        font.setPointSize(20)
        self.reg25.setFont(font)
        self.reg25.setCheckable(True)
        self.reg25.setFlat(True)
        self.reg25.setObjectName(_fromUtf8("reg25"))
        self.gridLayout_6.addWidget(self.reg25, 3, 2, 1, 1)
        self.read_reg2 = HexSpinBox(self.groupBox_14)
        self.read_reg2.setEnabled(False)
        self.read_reg2.setMaximum(255)
        self.read_reg2.setObjectName(_fromUtf8("read_reg2"))
        self.gridLayout_6.addWidget(self.read_reg2, 3, 9, 1, 1)
        self.readbtn_reg2 = QtWidgets.QPushButton(self.groupBox_14)
        self.readbtn_reg2.setObjectName(_fromUtf8("readbtn_reg2"))
        self.gridLayout_6.addWidget(self.readbtn_reg2, 3, 8, 1, 1)
        self.reg27 = QtWidgets.QPushButton(self.groupBox_14)
        self.reg27.setMinimumSize(QtCore.QSize(40, 0))
        font = QtGui.QFont()
        font.setPointSize(20)
        self.reg27.setFont(font)
        self.reg27.setCheckable(True)
        self.reg27.setFlat(True)
        self.reg27.setObjectName(_fromUtf8("reg27"))
        self.gridLayout_6.addWidget(self.reg27, 3, 0, 1, 1)
        self.reg23 = QtWidgets.QPushButton(self.groupBox_14)
        self.reg23.setMinimumSize(QtCore.QSize(40, 0))
        font = QtGui.QFont()
        font.setPointSize(20)
        self.reg23.setFont(font)
        self.reg23.setCheckable(True)
        self.reg23.setFlat(True)
        self.reg23.setObjectName(_fromUtf8("reg23"))
        self.gridLayout_6.addWidget(self.reg23, 3, 4, 1, 1)
        self.reg20 = QtWidgets.QPushButton(self.groupBox_14)
        self.reg20.setMinimumSize(QtCore.QSize(40, 0))
        font = QtGui.QFont()
        font.setPointSize(20)
        self.reg20.setFont(font)
        self.reg20.setCheckable(True)
        self.reg20.setFlat(True)
        self.reg20.setObjectName(_fromUtf8("reg20"))
        self.gridLayout_6.addWidget(self.reg20, 3, 7, 1, 1)
        self.reg21 = QtWidgets.QPushButton(self.groupBox_14)
        self.reg21.setMinimumSize(QtCore.QSize(40, 0))
        font = QtGui.QFont()
        font.setPointSize(20)
        self.reg21.setFont(font)
        self.reg21.setCheckable(True)
        self.reg21.setFlat(True)
        self.reg21.setObjectName(_fromUtf8("reg21"))
        self.gridLayout_6.addWidget(self.reg21, 3, 6, 1, 1)
        self.reg26 = QtWidgets.QPushButton(self.groupBox_14)
        self.reg26.setMinimumSize(QtCore.QSize(40, 0))
        font = QtGui.QFont()
        font.setPointSize(20)
        self.reg26.setFont(font)
        self.reg26.setCheckable(True)
        self.reg26.setFlat(True)
        self.reg26.setObjectName(_fromUtf8("reg26"))
        self.gridLayout_6.addWidget(self.reg26, 3, 1, 1, 1)
        self.writebtn_reg2 = QtWidgets.QPushButton(self.groupBox_14)
        self.writebtn_reg2.setObjectName(_fromUtf8("writebtn_reg2"))
        self.gridLayout_6.addWidget(self.writebtn_reg2, 3, 10, 1, 1)
        self.label_39 = QtWidgets.QLabel(self.groupBox_14)
        self.label_39.setAlignment(QtCore.Qt.AlignCenter)
        self.label_39.setObjectName(_fromUtf8("label_39"))
        self.gridLayout_6.addWidget(self.label_39, 1, 0, 1, 1)
        self.verticalLayout_3.addWidget(self.groupBox_14)
        self.groupBox_18 = QtWidgets.QGroupBox(self.tab_3)
        self.groupBox_18.setEnabled(False)
        self.groupBox_18.setObjectName(_fromUtf8("groupBox_18"))
        self.gridLayout_8 = QtWidgets.QGridLayout(self.groupBox_18)
        self.gridLayout_8.setObjectName(_fromUtf8("gridLayout_8"))
        self.writebtn_reg4 = QtWidgets.QPushButton(self.groupBox_18)
        self.writebtn_reg4.setObjectName(_fromUtf8("writebtn_reg4"))
        self.gridLayout_8.addWidget(self.writebtn_reg4, 2, 10, 1, 1)
        self.read_reg4 = HexSpinBox(self.groupBox_18)
        self.read_reg4.setEnabled(False)
        self.read_reg4.setMaximum(255)
        self.read_reg4.setObjectName(_fromUtf8("read_reg4"))
        self.gridLayout_8.addWidget(self.read_reg4, 2, 9, 1, 1)
        self.write_reg4 = HexSpinBox(self.groupBox_18)
        self.write_reg4.setMaximum(255)
        self.write_reg4.setObjectName(_fromUtf8("write_reg4"))
        self.gridLayout_8.addWidget(self.write_reg4, 2, 11, 1, 1)
        self.readbtn_reg4 = QtWidgets.QPushButton(self.groupBox_18)
        self.readbtn_reg4.setObjectName(_fromUtf8("readbtn_reg4"))
        self.gridLayout_8.addWidget(self.readbtn_reg4, 2, 8, 1, 1)
        self.label_55 = QtWidgets.QLabel(self.groupBox_18)
        self.label_55.setAlignment(QtCore.Qt.AlignCenter)
        self.label_55.setObjectName(_fromUtf8("label_55"))
        self.gridLayout_8.addWidget(self.label_55, 1, 0, 1, 1)
        self.label_53 = QtWidgets.QLabel(self.groupBox_18)
        self.label_53.setAlignment(QtCore.Qt.AlignCenter)
        self.label_53.setObjectName(_fromUtf8("label_53"))
        self.gridLayout_8.addWidget(self.label_53, 1, 1, 1, 1)
        self.label_56 = QtWidgets.QLabel(self.groupBox_18)
        self.label_56.setAlignment(QtCore.Qt.AlignCenter)
        self.label_56.setObjectName(_fromUtf8("label_56"))
        self.gridLayout_8.addWidget(self.label_56, 1, 2, 1, 1)
        self.label_52 = QtWidgets.QLabel(self.groupBox_18)
        self.label_52.setAlignment(QtCore.Qt.AlignCenter)
        self.label_52.setObjectName(_fromUtf8("label_52"))
        self.gridLayout_8.addWidget(self.label_52, 1, 3, 1, 1)
        self.label_49 = QtWidgets.QLabel(self.groupBox_18)
        self.label_49.setAlignment(QtCore.Qt.AlignCenter)
        self.label_49.setObjectName(_fromUtf8("label_49"))
        self.gridLayout_8.addWidget(self.label_49, 1, 4, 1, 1)
        self.label_54 = QtWidgets.QLabel(self.groupBox_18)
        self.label_54.setAlignment(QtCore.Qt.AlignCenter)
        self.label_54.setObjectName(_fromUtf8("label_54"))
        self.gridLayout_8.addWidget(self.label_54, 1, 5, 1, 1)
        self.label_51 = QtWidgets.QLabel(self.groupBox_18)
        self.label_51.setAlignment(QtCore.Qt.AlignCenter)
        self.label_51.setObjectName(_fromUtf8("label_51"))
        self.gridLayout_8.addWidget(self.label_51, 1, 6, 1, 1)
        self.label_50 = QtWidgets.QLabel(self.groupBox_18)
        self.label_50.setAlignment(QtCore.Qt.AlignCenter)
        self.label_50.setObjectName(_fromUtf8("label_50"))
        self.gridLayout_8.addWidget(self.label_50, 1, 7, 1, 1)
        self.reg47 = QtWidgets.QPushButton(self.groupBox_18)
        self.reg47.setMinimumSize(QtCore.QSize(40, 0))
        font = QtGui.QFont()
        font.setPointSize(20)
        self.reg47.setFont(font)
        self.reg47.setCheckable(True)
        self.reg47.setFlat(True)
        self.reg47.setObjectName(_fromUtf8("reg47"))
        self.gridLayout_8.addWidget(self.reg47, 2, 0, 1, 1)
        self.reg46 = QtWidgets.QPushButton(self.groupBox_18)
        self.reg46.setMinimumSize(QtCore.QSize(40, 0))
        font = QtGui.QFont()
        font.setPointSize(20)
        self.reg46.setFont(font)
        self.reg46.setCheckable(True)
        self.reg46.setFlat(True)
        self.reg46.setObjectName(_fromUtf8("reg46"))
        self.gridLayout_8.addWidget(self.reg46, 2, 1, 1, 1)
        self.reg45 = QtWidgets.QPushButton(self.groupBox_18)
        self.reg45.setMinimumSize(QtCore.QSize(40, 0))
        font = QtGui.QFont()
        font.setPointSize(20)
        self.reg45.setFont(font)
        self.reg45.setCheckable(True)
        self.reg45.setFlat(True)
        self.reg45.setObjectName(_fromUtf8("reg45"))
        self.gridLayout_8.addWidget(self.reg45, 2, 2, 1, 1)
        self.reg44 = QtWidgets.QPushButton(self.groupBox_18)
        self.reg44.setMinimumSize(QtCore.QSize(40, 0))
        font = QtGui.QFont()
        font.setPointSize(20)
        self.reg44.setFont(font)
        self.reg44.setCheckable(True)
        self.reg44.setFlat(True)
        self.reg44.setObjectName(_fromUtf8("reg44"))
        self.gridLayout_8.addWidget(self.reg44, 2, 3, 1, 1)
        self.reg43 = QtWidgets.QPushButton(self.groupBox_18)
        self.reg43.setMinimumSize(QtCore.QSize(40, 0))
        font = QtGui.QFont()
        font.setPointSize(20)
        self.reg43.setFont(font)
        self.reg43.setCheckable(True)
        self.reg43.setFlat(True)
        self.reg43.setObjectName(_fromUtf8("reg43"))
        self.gridLayout_8.addWidget(self.reg43, 2, 4, 1, 1)
        self.reg42 = QtWidgets.QPushButton(self.groupBox_18)
        self.reg42.setMinimumSize(QtCore.QSize(40, 0))
        font = QtGui.QFont()
        font.setPointSize(20)
        self.reg42.setFont(font)
        self.reg42.setCheckable(True)
        self.reg42.setFlat(True)
        self.reg42.setObjectName(_fromUtf8("reg42"))
        self.gridLayout_8.addWidget(self.reg42, 2, 5, 1, 1)
        self.reg41 = QtWidgets.QPushButton(self.groupBox_18)
        self.reg41.setMinimumSize(QtCore.QSize(40, 0))
        font = QtGui.QFont()
        font.setPointSize(20)
        self.reg41.setFont(font)
        self.reg41.setCheckable(True)
        self.reg41.setFlat(True)
        self.reg41.setObjectName(_fromUtf8("reg41"))
        self.gridLayout_8.addWidget(self.reg41, 2, 6, 1, 1)
        self.reg40 = QtWidgets.QPushButton(self.groupBox_18)
        self.reg40.setMinimumSize(QtCore.QSize(40, 0))
        font = QtGui.QFont()
        font.setPointSize(20)
        self.reg40.setFont(font)
        self.reg40.setCheckable(True)
        self.reg40.setFlat(True)
        self.reg40.setObjectName(_fromUtf8("reg40"))
        self.gridLayout_8.addWidget(self.reg40, 2, 7, 1, 1)
        self.verticalLayout_3.addWidget(self.groupBox_18)
        self.registers_tab.addTab(self.tab_3, _fromUtf8(""))
        self.tab_6 = QtWidgets.QWidget()
        self.tab_6.setObjectName(_fromUtf8("tab_6"))
        self.verticalLayout_12 = QtWidgets.QVBoxLayout(self.tab_6)
        self.verticalLayout_12.setObjectName(_fromUtf8("verticalLayout_12"))
        self.groupBox_17 = QtWidgets.QGroupBox(self.tab_6)
        self.groupBox_17.setEnabled(True)
        self.groupBox_17.setObjectName(_fromUtf8("groupBox_17"))
        self.gridLayout_9 = QtWidgets.QGridLayout(self.groupBox_17)
        self.gridLayout_9.setObjectName(_fromUtf8("gridLayout_9"))
        self.label_61 = QtWidgets.QLabel(self.groupBox_17)
        self.label_61.setAlignment(QtCore.Qt.AlignCenter)
        self.label_61.setObjectName(_fromUtf8("label_61"))
        self.gridLayout_9.addWidget(self.label_61, 0, 1, 1, 1)
        self.label_59 = QtWidgets.QLabel(self.groupBox_17)
        self.label_59.setAlignment(QtCore.Qt.AlignCenter)
        self.label_59.setObjectName(_fromUtf8("label_59"))
        self.gridLayout_9.addWidget(self.label_59, 0, 6, 1, 1)
        self.label_60 = QtWidgets.QLabel(self.groupBox_17)
        self.label_60.setAlignment(QtCore.Qt.AlignCenter)
        self.label_60.setObjectName(_fromUtf8("label_60"))
        self.gridLayout_9.addWidget(self.label_60, 0, 3, 1, 1)
        self.label_62 = QtWidgets.QLabel(self.groupBox_17)
        self.label_62.setAlignment(QtCore.Qt.AlignCenter)
        self.label_62.setObjectName(_fromUtf8("label_62"))
        self.gridLayout_9.addWidget(self.label_62, 0, 5, 1, 1)
        self.label_57 = QtWidgets.QLabel(self.groupBox_17)
        self.label_57.setAlignment(QtCore.Qt.AlignCenter)
        self.label_57.setObjectName(_fromUtf8("label_57"))
        self.gridLayout_9.addWidget(self.label_57, 0, 4, 1, 1)
        self.label_64 = QtWidgets.QLabel(self.groupBox_17)
        self.label_64.setAlignment(QtCore.Qt.AlignCenter)
        self.label_64.setObjectName(_fromUtf8("label_64"))
        self.gridLayout_9.addWidget(self.label_64, 0, 2, 1, 1)
        self.readbtn_reg5 = QtWidgets.QPushButton(self.groupBox_17)
        self.readbtn_reg5.setEnabled(True)
        self.readbtn_reg5.setObjectName(_fromUtf8("readbtn_reg5"))
        self.gridLayout_9.addWidget(self.readbtn_reg5, 1, 8, 1, 1)
        self.write_reg5 = HexSpinBox(self.groupBox_17)
        self.write_reg5.setEnabled(False)
        self.write_reg5.setMaximum(255)
        self.write_reg5.setObjectName(_fromUtf8("write_reg5"))
        self.gridLayout_9.addWidget(self.write_reg5, 1, 11, 1, 1)
        self.writebtn_reg5 = QtWidgets.QPushButton(self.groupBox_17)
        self.writebtn_reg5.setEnabled(True)
        self.writebtn_reg5.setObjectName(_fromUtf8("writebtn_reg5"))
        self.gridLayout_9.addWidget(self.writebtn_reg5, 1, 10, 1, 1)
        self.label_63 = QtWidgets.QLabel(self.groupBox_17)
        self.label_63.setAlignment(QtCore.Qt.AlignCenter)
        self.label_63.setObjectName(_fromUtf8("label_63"))
        self.gridLayout_9.addWidget(self.label_63, 0, 0, 1, 1)
        self.read_reg5 = HexSpinBox(self.groupBox_17)
        self.read_reg5.setEnabled(False)
        self.read_reg5.setMaximum(255)
        self.read_reg5.setObjectName(_fromUtf8("read_reg5"))
        self.gridLayout_9.addWidget(self.read_reg5, 1, 9, 1, 1)
        self.label_58 = QtWidgets.QLabel(self.groupBox_17)
        self.label_58.setAlignment(QtCore.Qt.AlignCenter)
        self.label_58.setObjectName(_fromUtf8("label_58"))
        self.gridLayout_9.addWidget(self.label_58, 0, 7, 1, 1)
        self.reg51 = QtWidgets.QPushButton(self.groupBox_17)
        self.reg51.setEnabled(False)
        self.reg51.setMinimumSize(QtCore.QSize(40, 0))
        font = QtGui.QFont()
        font.setPointSize(20)
        self.reg51.setFont(font)
        self.reg51.setCheckable(True)
        self.reg51.setFlat(True)
        self.reg51.setObjectName(_fromUtf8("reg51"))
        self.gridLayout_9.addWidget(self.reg51, 1, 6, 1, 1)
        self.reg52 = QtWidgets.QPushButton(self.groupBox_17)
        self.reg52.setEnabled(False)
        self.reg52.setMinimumSize(QtCore.QSize(40, 0))
        font = QtGui.QFont()
        font.setPointSize(20)
        self.reg52.setFont(font)
        self.reg52.setCheckable(True)
        self.reg52.setFlat(True)
        self.reg52.setObjectName(_fromUtf8("reg52"))
        self.gridLayout_9.addWidget(self.reg52, 1, 5, 1, 1)
        self.reg53 = QtWidgets.QPushButton(self.groupBox_17)
        self.reg53.setEnabled(False)
        self.reg53.setMinimumSize(QtCore.QSize(40, 0))
        font = QtGui.QFont()
        font.setPointSize(20)
        self.reg53.setFont(font)
        self.reg53.setCheckable(True)
        self.reg53.setFlat(True)
        self.reg53.setObjectName(_fromUtf8("reg53"))
        self.gridLayout_9.addWidget(self.reg53, 1, 4, 1, 1)
        self.reg54 = QtWidgets.QPushButton(self.groupBox_17)
        self.reg54.setEnabled(False)
        self.reg54.setMinimumSize(QtCore.QSize(40, 0))
        font = QtGui.QFont()
        font.setPointSize(20)
        self.reg54.setFont(font)
        self.reg54.setCheckable(True)
        self.reg54.setFlat(True)
        self.reg54.setObjectName(_fromUtf8("reg54"))
        self.gridLayout_9.addWidget(self.reg54, 1, 3, 1, 1)
        self.reg55 = QtWidgets.QPushButton(self.groupBox_17)
        self.reg55.setEnabled(False)
        self.reg55.setMinimumSize(QtCore.QSize(40, 0))
        font = QtGui.QFont()
        font.setPointSize(20)
        self.reg55.setFont(font)
        self.reg55.setCheckable(True)
        self.reg55.setFlat(True)
        self.reg55.setObjectName(_fromUtf8("reg55"))
        self.gridLayout_9.addWidget(self.reg55, 1, 2, 1, 1)
        self.reg56 = QtWidgets.QPushButton(self.groupBox_17)
        self.reg56.setEnabled(False)
        self.reg56.setMinimumSize(QtCore.QSize(40, 0))
        font = QtGui.QFont()
        font.setPointSize(20)
        self.reg56.setFont(font)
        self.reg56.setCheckable(True)
        self.reg56.setFlat(True)
        self.reg56.setObjectName(_fromUtf8("reg56"))
        self.gridLayout_9.addWidget(self.reg56, 1, 1, 1, 1)
        self.reg57 = QtWidgets.QPushButton(self.groupBox_17)
        self.reg57.setEnabled(False)
        self.reg57.setMinimumSize(QtCore.QSize(40, 0))
        font = QtGui.QFont()
        font.setPointSize(20)
        self.reg57.setFont(font)
        self.reg57.setCheckable(True)
        self.reg57.setFlat(True)
        self.reg57.setObjectName(_fromUtf8("reg57"))
        self.gridLayout_9.addWidget(self.reg57, 1, 0, 1, 1)
        self.reg50 = QtWidgets.QPushButton(self.groupBox_17)
        self.reg50.setEnabled(False)
        self.reg50.setMinimumSize(QtCore.QSize(40, 0))
        font = QtGui.QFont()
        font.setPointSize(20)
        self.reg50.setFont(font)
        self.reg50.setCheckable(True)
        self.reg50.setFlat(True)
        self.reg50.setObjectName(_fromUtf8("reg50"))
        self.gridLayout_9.addWidget(self.reg50, 1, 7, 1, 1)
        self.verticalLayout_12.addWidget(self.groupBox_17)
        self.groupBox_4 = QtWidgets.QGroupBox(self.tab_6)
        self.groupBox_4.setTitle(_fromUtf8(""))
        self.groupBox_4.setObjectName(_fromUtf8("groupBox_4"))
        self.gridLayout_4 = QtWidgets.QGridLayout(self.groupBox_4)
        self.gridLayout_4.setObjectName(_fromUtf8("gridLayout_4"))
        self.groupBox_11 = QtWidgets.QGroupBox(self.groupBox_4)
        self.groupBox_11.setObjectName(_fromUtf8("groupBox_11"))
        self.verticalLayout_18 = QtWidgets.QVBoxLayout(self.groupBox_11)
        self.verticalLayout_18.setObjectName(_fromUtf8("verticalLayout_18"))
        self.speed_CH1 = QtWidgets.QSpinBox(self.groupBox_11)
        self.speed_CH1.setEnabled(True)
        self.speed_CH1.setMinimum(2)
        self.speed_CH1.setMaximum(8)
        self.speed_CH1.setSingleStep(2)
        self.speed_CH1.setProperty("value", 8)
        self.speed_CH1.setObjectName(_fromUtf8("speed_CH1"))
        self.verticalLayout_18.addWidget(self.speed_CH1)
        self.gridLayout_4.addWidget(self.groupBox_11, 0, 0, 1, 1)
        self.groupBox_19 = QtWidgets.QGroupBox(self.groupBox_4)
        self.groupBox_19.setObjectName(_fromUtf8("groupBox_19"))
        self.verticalLayout_19 = QtWidgets.QVBoxLayout(self.groupBox_19)
        self.verticalLayout_19.setObjectName(_fromUtf8("verticalLayout_19"))
        self.speed_CH2 = QtWidgets.QSpinBox(self.groupBox_19)
        self.speed_CH2.setEnabled(True)
        self.speed_CH2.setMinimum(1)
        self.speed_CH2.setMaximum(4)
        self.speed_CH2.setProperty("value", 4)
        self.speed_CH2.setObjectName(_fromUtf8("speed_CH2"))
        self.verticalLayout_19.addWidget(self.speed_CH2)
        self.gridLayout_4.addWidget(self.groupBox_19, 0, 1, 1, 1)
        self.groupBox_20 = QtWidgets.QGroupBox(self.groupBox_4)
        self.groupBox_20.setObjectName(_fromUtf8("groupBox_20"))
        self.verticalLayout_20 = QtWidgets.QVBoxLayout(self.groupBox_20)
        self.verticalLayout_20.setObjectName(_fromUtf8("verticalLayout_20"))
        self.speed_CH3 = QtWidgets.QSpinBox(self.groupBox_20)
        self.speed_CH3.setEnabled(True)
        self.speed_CH3.setMinimum(1)
        self.speed_CH3.setMaximum(4)
        self.speed_CH3.setProperty("value", 4)
        self.speed_CH3.setObjectName(_fromUtf8("speed_CH3"))
        self.verticalLayout_20.addWidget(self.speed_CH3)
        self.gridLayout_4.addWidget(self.groupBox_20, 0, 2, 1, 1)
        self.groupBox_21 = QtWidgets.QGroupBox(self.groupBox_4)
        self.groupBox_21.setObjectName(_fromUtf8("groupBox_21"))
        self.verticalLayout_21 = QtWidgets.QVBoxLayout(self.groupBox_21)
        self.verticalLayout_21.setObjectName(_fromUtf8("verticalLayout_21"))
        self.speed_CH4 = QtWidgets.QSpinBox(self.groupBox_21)
        self.speed_CH4.setEnabled(True)
        self.speed_CH4.setMinimum(1)
        self.speed_CH4.setMaximum(4)
        self.speed_CH4.setProperty("value", 4)
        self.speed_CH4.setObjectName(_fromUtf8("speed_CH4"))
        self.verticalLayout_21.addWidget(self.speed_CH4)
        self.gridLayout_4.addWidget(self.groupBox_21, 0, 3, 1, 1)
        self.verticalLayout_12.addWidget(self.groupBox_4)
        self.registers_tab.addTab(self.tab_6, _fromUtf8(""))
        self.tab_7 = QtWidgets.QWidget()
        self.tab_7.setObjectName(_fromUtf8("tab_7"))
        self.verticalLayout_13 = QtWidgets.QVBoxLayout(self.tab_7)
        self.verticalLayout_13.setObjectName(_fromUtf8("verticalLayout_13"))
        self.groupBox_16 = QtWidgets.QGroupBox(self.tab_7)
        self.groupBox_16.setEnabled(True)
        self.groupBox_16.setObjectName(_fromUtf8("groupBox_16"))
        self.gridLayout_10 = QtWidgets.QGridLayout(self.groupBox_16)
        self.gridLayout_10.setObjectName(_fromUtf8("gridLayout_10"))
        self.writebtn_reg6 = QtWidgets.QPushButton(self.groupBox_16)
        self.writebtn_reg6.setEnabled(True)
        self.writebtn_reg6.setObjectName(_fromUtf8("writebtn_reg6"))
        self.gridLayout_10.addWidget(self.writebtn_reg6, 1, 10, 1, 1)
        self.read_reg6 = HexSpinBox(self.groupBox_16)
        self.read_reg6.setEnabled(False)
        self.read_reg6.setMaximum(255)
        self.read_reg6.setObjectName(_fromUtf8("read_reg6"))
        self.gridLayout_10.addWidget(self.read_reg6, 1, 9, 1, 1)
        self.write_reg6 = HexSpinBox(self.groupBox_16)
        self.write_reg6.setEnabled(False)
        self.write_reg6.setMaximum(255)
        self.write_reg6.setObjectName(_fromUtf8("write_reg6"))
        self.gridLayout_10.addWidget(self.write_reg6, 1, 11, 1, 1)
        self.readbtn_reg6 = QtWidgets.QPushButton(self.groupBox_16)
        self.readbtn_reg6.setEnabled(True)
        self.readbtn_reg6.setObjectName(_fromUtf8("readbtn_reg6"))
        self.gridLayout_10.addWidget(self.readbtn_reg6, 1, 8, 1, 1)
        self.label_71 = QtWidgets.QLabel(self.groupBox_16)
        self.label_71.setAlignment(QtCore.Qt.AlignCenter)
        self.label_71.setObjectName(_fromUtf8("label_71"))
        self.gridLayout_10.addWidget(self.label_71, 0, 0, 1, 1)
        self.label_69 = QtWidgets.QLabel(self.groupBox_16)
        self.label_69.setAlignment(QtCore.Qt.AlignCenter)
        self.label_69.setObjectName(_fromUtf8("label_69"))
        self.gridLayout_10.addWidget(self.label_69, 0, 1, 1, 1)
        self.label_72 = QtWidgets.QLabel(self.groupBox_16)
        self.label_72.setAlignment(QtCore.Qt.AlignCenter)
        self.label_72.setObjectName(_fromUtf8("label_72"))
        self.gridLayout_10.addWidget(self.label_72, 0, 2, 1, 1)
        self.label_68 = QtWidgets.QLabel(self.groupBox_16)
        self.label_68.setAlignment(QtCore.Qt.AlignCenter)
        self.label_68.setObjectName(_fromUtf8("label_68"))
        self.gridLayout_10.addWidget(self.label_68, 0, 3, 1, 1)
        self.label_65 = QtWidgets.QLabel(self.groupBox_16)
        self.label_65.setAlignment(QtCore.Qt.AlignCenter)
        self.label_65.setObjectName(_fromUtf8("label_65"))
        self.gridLayout_10.addWidget(self.label_65, 0, 4, 1, 1)
        self.label_70 = QtWidgets.QLabel(self.groupBox_16)
        self.label_70.setAlignment(QtCore.Qt.AlignCenter)
        self.label_70.setObjectName(_fromUtf8("label_70"))
        self.gridLayout_10.addWidget(self.label_70, 0, 5, 1, 1)
        self.label_67 = QtWidgets.QLabel(self.groupBox_16)
        self.label_67.setAlignment(QtCore.Qt.AlignCenter)
        self.label_67.setObjectName(_fromUtf8("label_67"))
        self.gridLayout_10.addWidget(self.label_67, 0, 6, 1, 1)
        self.label_66 = QtWidgets.QLabel(self.groupBox_16)
        self.label_66.setAlignment(QtCore.Qt.AlignCenter)
        self.label_66.setObjectName(_fromUtf8("label_66"))
        self.gridLayout_10.addWidget(self.label_66, 0, 7, 1, 1)
        self.reg67 = QtWidgets.QPushButton(self.groupBox_16)
        self.reg67.setEnabled(False)
        self.reg67.setMinimumSize(QtCore.QSize(40, 0))
        font = QtGui.QFont()
        font.setPointSize(20)
        self.reg67.setFont(font)
        self.reg67.setCheckable(True)
        self.reg67.setFlat(True)
        self.reg67.setObjectName(_fromUtf8("reg67"))
        self.gridLayout_10.addWidget(self.reg67, 1, 0, 1, 1)
        self.reg66 = QtWidgets.QPushButton(self.groupBox_16)
        self.reg66.setEnabled(False)
        self.reg66.setMinimumSize(QtCore.QSize(40, 0))
        font = QtGui.QFont()
        font.setPointSize(20)
        self.reg66.setFont(font)
        self.reg66.setCheckable(True)
        self.reg66.setFlat(True)
        self.reg66.setObjectName(_fromUtf8("reg66"))
        self.gridLayout_10.addWidget(self.reg66, 1, 1, 1, 1)
        self.reg65 = QtWidgets.QPushButton(self.groupBox_16)
        self.reg65.setEnabled(False)
        self.reg65.setMinimumSize(QtCore.QSize(40, 0))
        font = QtGui.QFont()
        font.setPointSize(20)
        self.reg65.setFont(font)
        self.reg65.setCheckable(True)
        self.reg65.setFlat(True)
        self.reg65.setObjectName(_fromUtf8("reg65"))
        self.gridLayout_10.addWidget(self.reg65, 1, 2, 1, 1)
        self.reg64 = QtWidgets.QPushButton(self.groupBox_16)
        self.reg64.setEnabled(False)
        self.reg64.setMinimumSize(QtCore.QSize(40, 0))
        font = QtGui.QFont()
        font.setPointSize(20)
        self.reg64.setFont(font)
        self.reg64.setCheckable(True)
        self.reg64.setFlat(True)
        self.reg64.setObjectName(_fromUtf8("reg64"))
        self.gridLayout_10.addWidget(self.reg64, 1, 3, 1, 1)
        self.reg63 = QtWidgets.QPushButton(self.groupBox_16)
        self.reg63.setEnabled(False)
        self.reg63.setMinimumSize(QtCore.QSize(40, 0))
        font = QtGui.QFont()
        font.setPointSize(20)
        self.reg63.setFont(font)
        self.reg63.setCheckable(True)
        self.reg63.setFlat(True)
        self.reg63.setObjectName(_fromUtf8("reg63"))
        self.gridLayout_10.addWidget(self.reg63, 1, 4, 1, 1)
        self.reg62 = QtWidgets.QPushButton(self.groupBox_16)
        self.reg62.setEnabled(False)
        self.reg62.setMinimumSize(QtCore.QSize(40, 0))
        font = QtGui.QFont()
        font.setPointSize(20)
        self.reg62.setFont(font)
        self.reg62.setCheckable(True)
        self.reg62.setFlat(True)
        self.reg62.setObjectName(_fromUtf8("reg62"))
        self.gridLayout_10.addWidget(self.reg62, 1, 5, 1, 1)
        self.reg61 = QtWidgets.QPushButton(self.groupBox_16)
        self.reg61.setEnabled(False)
        self.reg61.setMinimumSize(QtCore.QSize(40, 0))
        font = QtGui.QFont()
        font.setPointSize(20)
        self.reg61.setFont(font)
        self.reg61.setCheckable(True)
        self.reg61.setFlat(True)
        self.reg61.setObjectName(_fromUtf8("reg61"))
        self.gridLayout_10.addWidget(self.reg61, 1, 6, 1, 1)
        self.reg60 = QtWidgets.QPushButton(self.groupBox_16)
        self.reg60.setEnabled(False)
        self.reg60.setMinimumSize(QtCore.QSize(40, 0))
        font = QtGui.QFont()
        font.setPointSize(20)
        self.reg60.setFont(font)
        self.reg60.setCheckable(True)
        self.reg60.setFlat(True)
        self.reg60.setObjectName(_fromUtf8("reg60"))
        self.gridLayout_10.addWidget(self.reg60, 1, 7, 1, 1)
        self.verticalLayout_13.addWidget(self.groupBox_16)
        self.groupBox_3 = QtWidgets.QGroupBox(self.tab_7)
        self.groupBox_3.setTitle(_fromUtf8(""))
        self.groupBox_3.setObjectName(_fromUtf8("groupBox_3"))
        self.gridLayout_5 = QtWidgets.QGridLayout(self.groupBox_3)
        self.gridLayout_5.setObjectName(_fromUtf8("gridLayout_5"))
        self.groupBox_5 = QtWidgets.QGroupBox(self.groupBox_3)
        self.groupBox_5.setObjectName(_fromUtf8("groupBox_5"))
        self.verticalLayout_4 = QtWidgets.QVBoxLayout(self.groupBox_5)
        self.verticalLayout_4.setObjectName(_fromUtf8("verticalLayout_4"))
        self.sped_SPI = QtWidgets.QSpinBox(self.groupBox_5)
        self.sped_SPI.setEnabled(True)
        self.sped_SPI.setMinimum(1)
        self.sped_SPI.setMaximum(8)
        self.sped_SPI.setProperty("value", 8)
        self.sped_SPI.setObjectName(_fromUtf8("sped_SPI"))
        self.verticalLayout_4.addWidget(self.sped_SPI)
        self.gridLayout_5.addWidget(self.groupBox_5, 0, 0, 1, 1)
        self.groupBox_7 = QtWidgets.QGroupBox(self.groupBox_3)
        self.groupBox_7.setObjectName(_fromUtf8("groupBox_7"))
        self.verticalLayout_16 = QtWidgets.QVBoxLayout(self.groupBox_7)
        self.verticalLayout_16.setObjectName(_fromUtf8("verticalLayout_16"))
        self.cpha_SPI = QtWidgets.QSpinBox(self.groupBox_7)
        self.cpha_SPI.setEnabled(True)
        self.cpha_SPI.setMaximum(1)
        self.cpha_SPI.setObjectName(_fromUtf8("cpha_SPI"))
        self.verticalLayout_16.addWidget(self.cpha_SPI)
        self.gridLayout_5.addWidget(self.groupBox_7, 0, 4, 1, 1)
        self.groupBox_6 = QtWidgets.QGroupBox(self.groupBox_3)
        self.groupBox_6.setObjectName(_fromUtf8("groupBox_6"))
        self.verticalLayout_15 = QtWidgets.QVBoxLayout(self.groupBox_6)
        self.verticalLayout_15.setObjectName(_fromUtf8("verticalLayout_15"))
        self.cpol_SPI = QtWidgets.QSpinBox(self.groupBox_6)
        self.cpol_SPI.setEnabled(True)
        self.cpol_SPI.setMaximum(1)
        self.cpol_SPI.setObjectName(_fromUtf8("cpol_SPI"))
        self.verticalLayout_15.addWidget(self.cpol_SPI)
        self.gridLayout_5.addWidget(self.groupBox_6, 0, 3, 1, 1)
        self.groupBox_10 = QtWidgets.QGroupBox(self.groupBox_3)
        self.groupBox_10.setObjectName(_fromUtf8("groupBox_10"))
        self.horizontalLayout_4 = QtWidgets.QHBoxLayout(self.groupBox_10)
        self.horizontalLayout_4.setObjectName(_fromUtf8("horizontalLayout_4"))
        self.epol_SPI = QtWidgets.QComboBox(self.groupBox_10)
        self.epol_SPI.setObjectName(_fromUtf8("epol_SPI"))
        self.epol_SPI.addItem(_fromUtf8(""))
        self.epol_SPI.addItem(_fromUtf8(""))
        self.horizontalLayout_4.addWidget(self.epol_SPI)
        self.gridLayout_5.addWidget(self.groupBox_10, 0, 1, 1, 1)
        self.groupBox_9 = QtWidgets.QGroupBox(self.groupBox_3)
        self.groupBox_9.setObjectName(_fromUtf8("groupBox_9"))
        self.verticalLayout_17 = QtWidgets.QVBoxLayout(self.groupBox_9)
        self.verticalLayout_17.setObjectName(_fromUtf8("verticalLayout_17"))
        self.bits_SPI = QtWidgets.QComboBox(self.groupBox_9)
        self.bits_SPI.setEnabled(False)
        self.bits_SPI.setObjectName(_fromUtf8("bits_SPI"))
        self.bits_SPI.addItem(_fromUtf8(""))
        self.bits_SPI.addItem(_fromUtf8(""))
        self.verticalLayout_17.addWidget(self.bits_SPI)
        self.gridLayout_5.addWidget(self.groupBox_9, 0, 2, 1, 1)
        self.verticalLayout_13.addWidget(self.groupBox_3)
        self.registers_tab.addTab(self.tab_7, _fromUtf8(""))
        self.tab_8 = QtWidgets.QWidget()
        self.tab_8.setObjectName(_fromUtf8("tab_8"))
        self.verticalLayout_14 = QtWidgets.QVBoxLayout(self.tab_8)
        self.verticalLayout_14.setObjectName(_fromUtf8("verticalLayout_14"))
        self.groupBox_15 = QtWidgets.QGroupBox(self.tab_8)
        self.groupBox_15.setEnabled(False)
        self.groupBox_15.setObjectName(_fromUtf8("groupBox_15"))
        self.gridLayout_11 = QtWidgets.QGridLayout(self.groupBox_15)
        self.gridLayout_11.setObjectName(_fromUtf8("gridLayout_11"))
        self.readbtn_reg7 = QtWidgets.QPushButton(self.groupBox_15)
        self.readbtn_reg7.setObjectName(_fromUtf8("readbtn_reg7"))
        self.gridLayout_11.addWidget(self.readbtn_reg7, 2, 8, 1, 1)
        self.write_reg7 = HexSpinBox(self.groupBox_15)
        self.write_reg7.setMaximum(255)
        self.write_reg7.setObjectName(_fromUtf8("write_reg7"))
        self.gridLayout_11.addWidget(self.write_reg7, 2, 11, 1, 1)
        self.read_reg7 = HexSpinBox(self.groupBox_15)
        self.read_reg7.setEnabled(False)
        self.read_reg7.setMaximum(255)
        self.read_reg7.setObjectName(_fromUtf8("read_reg7"))
        self.gridLayout_11.addWidget(self.read_reg7, 2, 9, 1, 1)
        self.writebtn_reg7 = QtWidgets.QPushButton(self.groupBox_15)
        self.writebtn_reg7.setObjectName(_fromUtf8("writebtn_reg7"))
        self.gridLayout_11.addWidget(self.writebtn_reg7, 2, 10, 1, 1)
        self.label_79 = QtWidgets.QLabel(self.groupBox_15)
        self.label_79.setAlignment(QtCore.Qt.AlignCenter)
        self.label_79.setObjectName(_fromUtf8("label_79"))
        self.gridLayout_11.addWidget(self.label_79, 1, 0, 1, 1)
        self.label_77 = QtWidgets.QLabel(self.groupBox_15)
        self.label_77.setAlignment(QtCore.Qt.AlignCenter)
        self.label_77.setObjectName(_fromUtf8("label_77"))
        self.gridLayout_11.addWidget(self.label_77, 1, 1, 1, 1)
        self.label_80 = QtWidgets.QLabel(self.groupBox_15)
        self.label_80.setAlignment(QtCore.Qt.AlignCenter)
        self.label_80.setObjectName(_fromUtf8("label_80"))
        self.gridLayout_11.addWidget(self.label_80, 1, 2, 1, 1)
        self.label_76 = QtWidgets.QLabel(self.groupBox_15)
        self.label_76.setAlignment(QtCore.Qt.AlignCenter)
        self.label_76.setObjectName(_fromUtf8("label_76"))
        self.gridLayout_11.addWidget(self.label_76, 1, 3, 1, 1)
        self.label_73 = QtWidgets.QLabel(self.groupBox_15)
        self.label_73.setAlignment(QtCore.Qt.AlignCenter)
        self.label_73.setObjectName(_fromUtf8("label_73"))
        self.gridLayout_11.addWidget(self.label_73, 1, 4, 1, 1)
        self.label_78 = QtWidgets.QLabel(self.groupBox_15)
        self.label_78.setAlignment(QtCore.Qt.AlignCenter)
        self.label_78.setObjectName(_fromUtf8("label_78"))
        self.gridLayout_11.addWidget(self.label_78, 1, 5, 1, 1)
        self.label_75 = QtWidgets.QLabel(self.groupBox_15)
        self.label_75.setAlignment(QtCore.Qt.AlignCenter)
        self.label_75.setObjectName(_fromUtf8("label_75"))
        self.gridLayout_11.addWidget(self.label_75, 1, 6, 1, 1)
        self.label_74 = QtWidgets.QLabel(self.groupBox_15)
        self.label_74.setAlignment(QtCore.Qt.AlignCenter)
        self.label_74.setObjectName(_fromUtf8("label_74"))
        self.gridLayout_11.addWidget(self.label_74, 1, 7, 1, 1)
        self.reg77 = QtWidgets.QPushButton(self.groupBox_15)
        self.reg77.setMinimumSize(QtCore.QSize(40, 0))
        font = QtGui.QFont()
        font.setPointSize(20)
        self.reg77.setFont(font)
        self.reg77.setCheckable(True)
        self.reg77.setFlat(True)
        self.reg77.setObjectName(_fromUtf8("reg77"))
        self.gridLayout_11.addWidget(self.reg77, 2, 0, 1, 1)
        self.reg76 = QtWidgets.QPushButton(self.groupBox_15)
        self.reg76.setMinimumSize(QtCore.QSize(40, 0))
        font = QtGui.QFont()
        font.setPointSize(20)
        self.reg76.setFont(font)
        self.reg76.setCheckable(True)
        self.reg76.setFlat(True)
        self.reg76.setObjectName(_fromUtf8("reg76"))
        self.gridLayout_11.addWidget(self.reg76, 2, 1, 1, 1)
        self.reg75 = QtWidgets.QPushButton(self.groupBox_15)
        self.reg75.setMinimumSize(QtCore.QSize(40, 0))
        font = QtGui.QFont()
        font.setPointSize(20)
        self.reg75.setFont(font)
        self.reg75.setCheckable(True)
        self.reg75.setFlat(True)
        self.reg75.setObjectName(_fromUtf8("reg75"))
        self.gridLayout_11.addWidget(self.reg75, 2, 2, 1, 1)
        self.reg74 = QtWidgets.QPushButton(self.groupBox_15)
        self.reg74.setMinimumSize(QtCore.QSize(40, 0))
        font = QtGui.QFont()
        font.setPointSize(20)
        self.reg74.setFont(font)
        self.reg74.setCheckable(True)
        self.reg74.setFlat(True)
        self.reg74.setObjectName(_fromUtf8("reg74"))
        self.gridLayout_11.addWidget(self.reg74, 2, 3, 1, 1)
        self.reg73 = QtWidgets.QPushButton(self.groupBox_15)
        self.reg73.setMinimumSize(QtCore.QSize(40, 0))
        font = QtGui.QFont()
        font.setPointSize(20)
        self.reg73.setFont(font)
        self.reg73.setCheckable(True)
        self.reg73.setFlat(True)
        self.reg73.setObjectName(_fromUtf8("reg73"))
        self.gridLayout_11.addWidget(self.reg73, 2, 4, 1, 1)
        self.reg72 = QtWidgets.QPushButton(self.groupBox_15)
        self.reg72.setMinimumSize(QtCore.QSize(40, 0))
        font = QtGui.QFont()
        font.setPointSize(20)
        self.reg72.setFont(font)
        self.reg72.setCheckable(True)
        self.reg72.setFlat(True)
        self.reg72.setObjectName(_fromUtf8("reg72"))
        self.gridLayout_11.addWidget(self.reg72, 2, 5, 1, 1)
        self.reg71 = QtWidgets.QPushButton(self.groupBox_15)
        self.reg71.setMinimumSize(QtCore.QSize(40, 0))
        font = QtGui.QFont()
        font.setPointSize(20)
        self.reg71.setFont(font)
        self.reg71.setCheckable(True)
        self.reg71.setFlat(True)
        self.reg71.setObjectName(_fromUtf8("reg71"))
        self.gridLayout_11.addWidget(self.reg71, 2, 6, 1, 1)
        self.reg70 = QtWidgets.QPushButton(self.groupBox_15)
        self.reg70.setMinimumSize(QtCore.QSize(40, 0))
        font = QtGui.QFont()
        font.setPointSize(20)
        self.reg70.setFont(font)
        self.reg70.setCheckable(True)
        self.reg70.setFlat(True)
        self.reg70.setObjectName(_fromUtf8("reg70"))
        self.gridLayout_11.addWidget(self.reg70, 2, 7, 1, 1)
        self.verticalLayout_14.addWidget(self.groupBox_15)
        self.groupBox_2 = QtWidgets.QGroupBox(self.tab_8)
        self.groupBox_2.setTitle(_fromUtf8(""))
        self.groupBox_2.setObjectName(_fromUtf8("groupBox_2"))
        self.verticalLayout_14.addWidget(self.groupBox_2)
        self.registers_tab.addTab(self.tab_8, _fromUtf8(""))
        self.verticalLayout_2.addWidget(self.registers_tab)
        self.gridLayout.addWidget(self.regixters_box, 3, 0, 1, 1)

        self.retranslateUi(Form)
        self.portList.setCurrentIndex(-1)
        self.registers_tab.setCurrentIndex(0)
        QtCore.QMetaObject.connectSlotsByName(Form)

    def retranslateUi(self, Form):
        Form.setWindowTitle(_translate("Form", "TinyI2C", None))
        self.conport_box.setTitle(_translate("Form", "COM port", None))
        self.getPortBtn.setText(_translate("Form", "Search", None))
        self.log_box.setTitle(_translate("Form", "Log message", None))
        self.log_text.setPlainText(_translate("Form", "This is \n"
                                              "a\n"
                                              "log message\n"
                                              "window", None))
        self.i2c_box.setTitle(_translate("Form", "Interfaces", None))
        self.i2c1_box.setTitle(_translate("Form", "I2C0", None))
        self.readbtn_CH1.setText(_translate("Form", "Read", None))
        self.writebtn_CH1.setText(_translate("Form", "Write", None))
        self.i2c2_box.setTitle(_translate("Form", "I2C1", None))
        self.readbtn_CH2.setText(_translate("Form", "Read", None))
        self.writebtn_CH2.setText(_translate("Form", "Write", None))
        self.i2c3_box.setTitle(_translate("Form", "I2C2", None))
        self.readbtn_CH3.setText(_translate("Form", "Read", None))
        self.writebtn_CH3.setText(_translate("Form", "Write", None))
        self.i2c4_box.setTitle(_translate("Form", "I2C3", None))
        self.readbtn_CH4.setText(_translate("Form", "Read", None))
        self.writebtn_CH4.setText(_translate("Form", "Write", None))
        self.spi_box.setTitle(_translate("Form", "SPI", None))
        self.readbtn_SPI.setText(_translate("Form", "Read", None))
        self.writebtn_SPI.setText(_translate("Form", "Write", None))
        self.regixters_box.setTitle(_translate("Form", "Registers", None))
        self.reg0_box.setTitle(_translate("Form", "CHIP_ID (ro)", None))
        self.readbtn_reg0.setText(_translate("Form", "Read", None))
        self.writebtn_reg0.setText(_translate("Form", "Write", None))
        self.label_8.setText(_translate("Form", "[0]", None))
        self.label.setText(_translate("Form", "[7]", None))
        self.label_7.setText(_translate("Form", "[1]", None))
        self.label_6.setText(_translate("Form", "[2]", None))
        self.label_5.setText(_translate("Form", "[3]", None))
        self.label_4.setText(_translate("Form", "[4]", None))
        self.label_3.setText(_translate("Form", "[5]", None))
        self.label_2.setText(_translate("Form", "[6]", None))
        self.reg00.setText(_translate("Form", "0", None))
        self.reg01.setText(_translate("Form", "0", None))
        self.reg02.setText(_translate("Form", "0", None))
        self.reg03.setText(_translate("Form", "0", None))
        self.reg04.setText(_translate("Form", "0", None))
        self.reg05.setText(_translate("Form", "0", None))
        self.reg06.setText(_translate("Form", "0", None))
        self.reg07.setText(_translate("Form", "0", None))
        self.registers_tab.setTabText(self.registers_tab.indexOf(self.tab), _translate("Form", "CHIP_ID", None))
        self.reg1_box.setTitle(_translate("Form", "STATUS", None))
        self.label_15.setText(_translate("Form", "[7]", None))
        self.label_13.setText(_translate("Form", "[6]", None))
        self.label_16.setText(_translate("Form", "[5]", None))
        self.label_12.setText(_translate("Form", "[4]", None))
        self.label_9.setText(_translate("Form", "[3]", None))
        self.label_14.setText(_translate("Form", "[2]", None))
        self.label_11.setText(_translate("Form", "[1]", None))
        self.label_10.setText(_translate("Form", "[0]", None))
        self.reg17.setText(_translate("Form", "0", None))
        self.reg16.setText(_translate("Form", "0", None))
        self.reg15.setText(_translate("Form", "0", None))
        self.reg14.setText(_translate("Form", "0", None))
        self.reg13.setText(_translate("Form", "0", None))
        self.reg12.setText(_translate("Form", "0", None))
        self.reg11.setText(_translate("Form", "0", None))
        self.reg10.setText(_translate("Form", "0", None))
        self.readbtn_reg1.setText(_translate("Form", "Read", None))
        self.writebtn_reg1.setText(_translate("Form", "Write", None))
        self.reg3_box.setTitle(_translate("Form", "CONFIG", None))
        self.label_47.setText(_translate("Form", "[7]", None))
        self.label_48.setText(_translate("Form", "[5]", None))
        self.label_46.setText(_translate("Form", "[2]", None))
        self.reg36.setText(_translate("Form", "0", None))
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
        self.reg51.setText(_translate("Form", "0", None))
        self.reg52.setText(_translate("Form", "0", None))
        self.reg53.setText(_translate("Form", "0", None))
        self.reg54.setText(_translate("Form", "0", None))
        self.reg55.setText(_translate("Form", "0", None))
        self.reg56.setText(_translate("Form", "0", None))
        self.reg57.setText(_translate("Form", "0", None))
        self.reg50.setText(_translate("Form", "0", None))
        self.groupBox_11.setTitle(_translate("Form", "I2C0", None))
        self.speed_CH1.setSuffix(_translate("Form", "00kHz", None))
        self.groupBox_19.setTitle(_translate("Form", "I2C1", None))
        self.speed_CH2.setSuffix(_translate("Form", "00kHz", None))
        self.groupBox_20.setTitle(_translate("Form", "I2C2", None))
        self.speed_CH3.setSuffix(_translate("Form", "00kHz", None))
        self.groupBox_21.setTitle(_translate("Form", "I2C3", None))
        self.speed_CH4.setSuffix(_translate("Form", "00kHz", None))
        self.registers_tab.setTabText(self.registers_tab.indexOf(self.tab_6), _translate("Form", "I2C", None))
        self.groupBox_16.setTitle(_translate("Form", "SPI_CONF", None))
        self.writebtn_reg6.setText(_translate("Form", "Write", None))
        self.readbtn_reg6.setText(_translate("Form", "Read", None))
        self.label_71.setText(_translate("Form", "[7]", None))
        self.label_69.setText(_translate("Form", "[6]", None))
        self.label_72.setText(_translate("Form", "[5]", None))
        self.label_68.setText(_translate("Form", "[4]", None))
        self.label_65.setText(_translate("Form", "[3]", None))
        self.label_70.setText(_translate("Form", "[2]", None))
        self.label_67.setText(_translate("Form", "[1]", None))
        self.label_66.setText(_translate("Form", "[0]", None))
        self.reg67.setText(_translate("Form", "0", None))
        self.reg66.setText(_translate("Form", "0", None))
        self.reg65.setText(_translate("Form", "0", None))
        self.reg64.setText(_translate("Form", "0", None))
        self.reg63.setText(_translate("Form", "0", None))
        self.reg62.setText(_translate("Form", "0", None))
        self.reg61.setText(_translate("Form", "0", None))
        self.reg60.setText(_translate("Form", "0", None))
        self.groupBox_5.setTitle(_translate("Form", "SPEED", None))
        self.sped_SPI.setSuffix(_translate("Form", "MHz", None))
        self.groupBox_7.setTitle(_translate("Form", "CPHA", None))
        self.groupBox_6.setTitle(_translate("Form", "CPOL", None))
        self.groupBox_10.setTitle(_translate("Form", "SELECT POL", None))
        self.epol_SPI.setItemText(0, _translate("Form", "Low Active", None))
        self.epol_SPI.setItemText(1, _translate("Form", "High Active", None))
        self.groupBox_9.setTitle(_translate("Form", "LENGTH", None))
        self.bits_SPI.setItemText(0, _translate("Form", "8 bit", None))
        self.bits_SPI.setItemText(1, _translate("Form", "16 bit", None))
        self.registers_tab.setTabText(self.registers_tab.indexOf(self.tab_7), _translate("Form", "SPI", None))
        self.groupBox_15.setTitle(_translate("Form", "Register 7", None))
        self.readbtn_reg7.setText(_translate("Form", "Read", None))
        self.writebtn_reg7.setText(_translate("Form", "Write", None))
        self.label_79.setText(_translate("Form", "[7]", None))
        self.label_77.setText(_translate("Form", "[6]", None))
        self.label_80.setText(_translate("Form", "[5]", None))
        self.label_76.setText(_translate("Form", "[4]", None))
        self.label_73.setText(_translate("Form", "[3]", None))
        self.label_78.setText(_translate("Form", "[2]", None))
        self.label_75.setText(_translate("Form", "[1]", None))
        self.label_74.setText(_translate("Form", "[0]", None))
        self.reg77.setText(_translate("Form", "0", None))
        self.reg76.setText(_translate("Form", "0", None))
        self.reg75.setText(_translate("Form", "0", None))
        self.reg74.setText(_translate("Form", "0", None))
        self.reg73.setText(_translate("Form", "0", None))
        self.reg72.setText(_translate("Form", "0", None))
        self.reg71.setText(_translate("Form", "0", None))
        self.reg70.setText(_translate("Form", "0", None))
        self.registers_tab.setTabText(self.registers_tab.indexOf(self.tab_8), _translate("Form", "Unused7", None))

from hexSpinbox import HexSpinBox
